westphae/kingfisher/hardware/hat/meta/info.html

# Raspberry Pi HAT

## 40-pin Expansion Board

This project template forms the basis of an expansion board (HAT) for the Raspberry Pi (https://www.raspberrypi.org/) single board computers with a 40-pin GPIO header.
This includes the following models:

- Pi 1 Model A+/B+
- Pi 2 Model B
- Pi 3 Model A+/B/B+
- Pi 4 Model B

Note: for the Pi Zero (W) or smaller designs, see the RaspberryPi-uHAT template.

This project includes a PCB edge set according to the Raspberry Pi HAT Mechanical Specification (https://raw.githubusercontent.com/raspberrypi/hats/master/hat-board-mechanical.pdf) with connectors placed correctly to align the two boards. An alternate edge is included on the User.Drawings layer for the use with an SMT connector. Cutouts have also been defined for the camera and the display cables.

The schematic includes an ID EEPROM chip along with the necessary support components. It does not specify footprints for the ID EEPROM. It is up to the user to choose an appropriate EEPROM chip and footprints.

The official Raspberry Pi HAT Specification (https://github.com/raspberrypi/hats) includes additional information and a design guide.

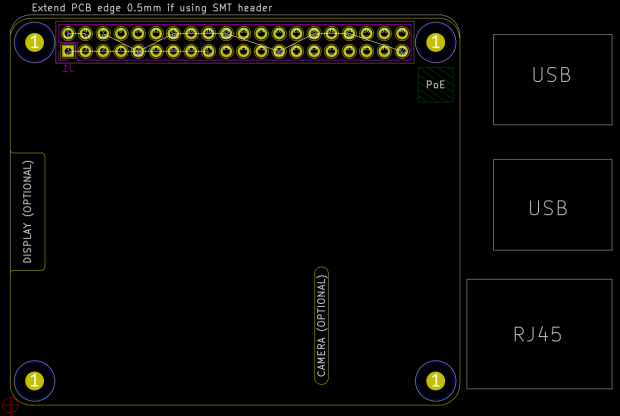
[picture p1: hardware/hat/meta/brd.png]


(c) 2021 Caleb Reister

Adapted from the raspberrypi-gpio-40pin template:
(c) 2016 Ashton Johnson
(c) 2016 Kicad Developers
