westphae/kingfisher/firmware/pod/src/sensors/bq27441.rs

//! SparkFun Battery Babysitter / TI BQ27441-G1A fuel gauge (I²C).
//!
//! Design Capacity and Design Energy are rewritten when ITPOR is set or when
//! the chip still has the G1A factory 1340 mAh. The G1A data memory is RAM-only,
//! so a battery unplug forgets it. Impedance Track initializes Qmax from Design
//! Capacity: Qmax_mAh = QmaxCell0 * DesignCap / 2^14, and Qmax Cell 0 defaults
//! to 16384 Num. Writing learned FCC into offset 0 left FullChargeCapacity
//! stuck at 1340. Default Design Cap is the chem-ID scale and must not change.

use embassy_time::{block_for, Duration, Instant};
use esp_println::println;

use super::bus::Bus as I2cBus;

pub const ADDR: u8 = 0x55;

const CMD_CONTROL: u8 = 0x00;
const CMD_VOLTAGE: u8 = 0x04;
const CMD_FLAGS: u8 = 0x06;
const CMD_REM_CAPACITY: u8 = 0x0c;
const CMD_FULL_CAPACITY: u8 = 0x0e;
const CMD_DESIGN_CAPACITY: u8 = 0x3c;
const CMD_AVG_CURRENT: u8 = 0x10;
const CMD_AVG_POWER: u8 = 0x18;
const CMD_SOC: u8 = 0x1c;

const CTRL_DEVICE_TYPE: u16 = 0x0001;
const CTRL_UNSEAL_KEY: u16 = 0x8000;
const CTRL_SET_CFGUPDATE: u16 = 0x0013;
const CTRL_SOFT_RESET: u16 = 0x0042;

const EXT_CONTROL: u8 = 0x61;
const EXT_DATACLASS: u8 = 0x3e;
const EXT_DATABLOCK: u8 = 0x3f;
const EXT_BLOCKDATA: u8 = 0x40;
const EXT_CHECKSUM: u8 = 0x60;

const ID_STATE: u8 = 82;
const DESIGN_CAPACITY_OFFSET: u8 = 10;
const DESIGN_ENERGY_OFFSET: u8 = 12;
const TERMINATE_VOLTAGE_OFFSET: u8 = 16;

const FLAG_BAT_DET: u16 = 1 << 3;
const CTRL_BAT_INSERT: u16 = 0x000C;

/// G1A ROM default Design Capacity. A matching 0x3C after ITPOR means the
/// host has not reloaded the pack size yet.
const G1A_FACTORY_DESIGN_MAH: u16 = 1340;

/// State subclass stores 16-bit fields MSB-first (TI TRM / SparkFun library).
fn u16_be_bytes(v: u16) -> [u8; 2] {
    [(v >> 8) as u8, (v & 0xff) as u8]
}

/// Design energy (mWh) from mAh at 3.7 V nominal LiPo.
fn design_energy_mwh(mah: u16) -> u16 {
    ((mah as u32) * 37 / 10) as u16
}

const DEVICE_ID: u16 = 0x0421;
const FLAG_ITPOR: u16 = 1 << 5;
const FLAG_CFGUPMODE: u16 = 1 << 4;

const I2C_GAP_US: u64 = 70;
const MIN_READ_INTERVAL_US: u64 = 500_000;

/// One fuel-gauge sample mapped to wire [`Reading::Battery`] units.
#[derive(Debug, Clone, Copy)]
pub struct Sample {
    pub voltage_v: f32,
    pub current_a: f32,
    pub power_w: f32,
    pub capacity_remain_mah: f32,
    pub capacity_full_mah: f32,
    pub soc_pct: f32,
    pub time_remain_s: f32,
    pub design_capacity_mah: u16,
}

pub struct Bq27441 {
    addr: u8,
    last_read_at: Option<Instant>,
}

impl Bq27441 {
    pub fn probe(bus: &mut I2cBus) -> Option<Self> {
        match read_control_word(bus, ADDR, CTRL_DEVICE_TYPE) {
            Ok(id) => {
                println!("pod: i2c 0x{ADDR:02x} device_type=0x{id:04x}");
                if id == DEVICE_ID {
                    return Some(Self {
                        addr: ADDR,
                        last_read_at: None,
                    });
                }
            }
            Err(e) => println!("pod: i2c 0x{ADDR:02x} device_type read: {:?}", e),
        }
        None
    }

    pub fn init(&mut self, bus: &mut I2cBus) -> Result<(), ()> {
        let flags = read_word(bus, self.addr, CMD_FLAGS)?;
        let fcc = read_word(bus, self.addr, CMD_FULL_CAPACITY)?;
        let design_reg = read_design_capacity(bus, self.addr)?;
        let itpor = flags & FLAG_ITPOR != 0;
        // Data memory is RAM: ITPOR means factory defaults (Design ~1340).
        // Restore the baked pack size; Hello can override. Do not write
        // State Qmax Cell 0 — IT seeds Qmax from Design Capacity.
        crate::battery_cfg::note_chip(design_reg);
        let seed = crate::battery_cfg::baked_default();
        // Missed ITPOR still leaves 0x3C at the G1A factory 1340. Treat that
        // as blank when the configured pack is a different size.
        let factory_leftover =
            design_reg == G1A_FACTORY_DESIGN_MAH && seed != G1A_FACTORY_DESIGN_MAH;
        if itpor || design_reg == 0 || factory_leftover {
            println!(
                "pod: bq27441 design_reg={design_reg} (itpor={itpor} fcc={fcc}); restoring design {seed} mAh"
            );
            let _ = crate::battery_cfg::request_design_mah(seed);
        } else {
            println!(
                "pod: bq27441 design capacity {design_reg} mAh (itpor={itpor} fcc={fcc}); trusting gauge RAM"
            );
        }
        self.last_read_at = None;
        println!("pod: bq27441 init ok");
        Ok(())
    }

    /// Reprogram Design Capacity and Design Energy (mAh / mWh) while running.
    /// `qmax_mah` is only for logs — State Qmax Cell 0 is not an mAh seed.
    pub fn program_capacity(&self, bus: &mut I2cBus, design_mah: u16, qmax_mah: u16) -> Result<(), ()> {
        set_capacity_params(bus, self.addr, design_mah, qmax_mah)
    }

    /// Read all headline metrics when the BQ27441 rate limit allows.
    pub fn read_when_due(&mut self, bus: &mut I2cBus) -> Result<Option<Sample>, ()> {
        let now = Instant::now();
        if let Some(prev) = self.last_read_at {
            if now.duration_since(prev).as_micros() < MIN_READ_INTERVAL_US {
                return Ok(None);
            }
        }
        let sample = self.read_sample(bus)?;
        self.last_read_at = Some(now);
        Ok(Some(sample))
    }

    fn read_sample(&self, bus: &mut I2cBus) -> Result<Sample, ()> {
        let voltage_mv = read_word(bus, self.addr, CMD_VOLTAGE)?;
        let capacity_remain = read_word(bus, self.addr, CMD_REM_CAPACITY)?;
        let capacity_full = read_word(bus, self.addr, CMD_FULL_CAPACITY)?;
        let current_ma = read_word_signed(bus, self.addr, CMD_AVG_CURRENT)?;
        let power_mw = read_word_signed(bus, self.addr, CMD_AVG_POWER)?;
        let soc = read_word(bus, self.addr, CMD_SOC)?;
        let design_capacity_mah = read_design_capacity(bus, self.addr)?;

        let voltage_v = voltage_mv as f32 / 1000.0;
        let current_a = current_ma as f32 / 1000.0;
        let power_w = power_mw as f32 / 1000.0;
        let capacity_remain_mah = capacity_remain as f32;
        let capacity_full_mah = capacity_full as f32;
        let soc_pct = soc as f32;

        // mAh / mA -> hours; ×3600 -> seconds (not mAh/A, which is 1000× too large).
        let time_remain_s = if current_ma < -1 {
            (capacity_remain_mah / (current_ma as f32).abs()) * 3600.0
        } else {
            -1.0
        };

        Ok(Sample {
            voltage_v,
            current_a,
            power_w,
            capacity_remain_mah,
            capacity_full_mah,
            soc_pct,
            time_remain_s,
            design_capacity_mah,
        })
    }
}

/// Minimal voltage/current read for the deep-sleep wake check: no init, no
/// rate limiting, no Sample plumbing. None when the gauge doesn't answer.
pub fn quick_check(bus: &mut I2cBus) -> Option<(f32, f32)> {
    let v = read_word(bus, ADDR, CMD_VOLTAGE).ok()?;
    let i = read_word_signed(bus, ADDR, CMD_AVG_CURRENT).ok()?;
    Some((v as f32 / 1000.0, i as f32 / 1000.0))
}

fn i2c_gap() {
    block_for(Duration::from_micros(I2C_GAP_US));
}

fn read_word(bus: &mut I2cBus, addr: u8, reg: u8) -> Result<u16, ()> {
    let mut buf = [0u8; 2];
    bus.write_read(addr, &[reg], &mut buf).map_err(|_| ())?;
    i2c_gap();
    Ok(u16::from_le_bytes(buf))
}

fn read_word_signed(bus: &mut I2cBus, addr: u8, reg: u8) -> Result<i16, ()> {
    Ok(read_word(bus, addr, reg)? as i16)
}

fn write_byte(bus: &mut I2cBus, addr: u8, reg: u8, val: u8) -> Result<(), ()> {
    bus.write(addr, &[reg, val]).map_err(|_| ())?;
    i2c_gap();
    Ok(())
}

fn read_byte(bus: &mut I2cBus, addr: u8, reg: u8) -> Result<u8, ()> {
    let mut buf = [0u8];
    bus.write_read(addr, &[reg], &mut buf).map_err(|_| ())?;
    i2c_gap();
    Ok(buf[0])
}

/// Data-memory Design Capacity (mAh), not learned FullChargeCapacity (0x0E).
fn read_design_capacity(bus: &mut I2cBus, addr: u8) -> Result<u16, ()> {
    read_word(bus, addr, CMD_DESIGN_CAPACITY)
}

fn read_control_word(bus: &mut I2cBus, addr: u8, function: u16) -> Result<u16, ()> {
    let cmd = function.to_le_bytes();
    bus.write(addr, &[CMD_CONTROL, cmd[0], cmd[1]])
        .map_err(|_| ())?;
    i2c_gap();
    read_word(bus, addr, CMD_CONTROL)
}

fn execute_control(bus: &mut I2cBus, addr: u8, function: u16) -> Result<(), ()> {
    let cmd = function.to_le_bytes();
    bus.write(addr, &[CMD_CONTROL, cmd[0], cmd[1]])
        .map_err(|_| ())?;
    i2c_gap();
    Ok(())
}

fn enter_config(bus: &mut I2cBus, addr: u8) -> Result<(), ()> {
    // Unseal twice (SparkFun/TI); required when the gauge is in sealed mode.
    execute_control(bus, addr, CTRL_UNSEAL_KEY)?;
    execute_control(bus, addr, CTRL_UNSEAL_KEY)?;
    execute_control(bus, addr, CTRL_SET_CFGUPDATE)?;
    for _ in 0..2000 {
        let flags = read_word(bus, addr, CMD_FLAGS)?;
        if flags & FLAG_CFGUPMODE != 0 {
            return Ok(());
        }
        block_for(Duration::from_millis(1));
    }
    Err(())
}

fn exit_config_resim(bus: &mut I2cBus, addr: u8) -> Result<(), ()> {
    execute_control(bus, addr, CTRL_SOFT_RESET)?;
    for _ in 0..2000 {
        let flags = read_word(bus, addr, CMD_FLAGS)?;
        if flags & FLAG_CFGUPMODE == 0 {
            return Ok(());
        }
        block_for(Duration::from_millis(1));
    }
    Err(())
}

fn read_block_window(bus: &mut I2cBus, addr: u8) -> Result<[u8; 32], ()> {
    let mut block = [0u8; 32];
    for (i, b) in block.iter_mut().enumerate() {
        *b = read_byte(bus, addr, EXT_BLOCKDATA + i as u8)?;
    }
    Ok(block)
}

fn select_data_block(bus: &mut I2cBus, addr: u8, class_id: u8, offset: u8) -> Result<(), ()> {
    write_byte(bus, addr, EXT_CONTROL, 0x00)?;
    write_byte(bus, addr, EXT_DATACLASS, class_id)?;
    write_byte(bus, addr, EXT_DATABLOCK, offset / 32)?;
    // TI: BlockDataClass must settle before the 32-byte window is valid.
    block_for(Duration::from_millis(5));
    Ok(())
}

fn set_capacity_params(bus: &mut I2cBus, addr: u8, design_mah: u16, qmax_mah: u16) -> Result<(), ()> {
    if enter_config(bus, addr).is_err() {
        log_program_fail(design_mah, qmax_mah, ProgramFail::EnterConfig, 0);
        return Err(());
    }
    if write_design_params(bus, addr, design_mah).is_err() {
        log_program_fail(design_mah, qmax_mah, ProgramFail::WriteBlock, 0);
        let _ = exit_config_resim(bus, addr);
        return Err(());
    }
    if exit_config_resim(bus, addr).is_err() {
        log_program_fail(design_mah, qmax_mah, ProgramFail::ExitConfig, 0);
        return Err(());
    }
    maybe_bat_insert(bus, addr);
    block_for(Duration::from_millis(500));
    for attempt in 0..40 {
        match read_design_capacity(bus, addr) {
            Ok(reg) if reg == design_mah => {
                let fcc = read_word(bus, addr, CMD_FULL_CAPACITY).unwrap_or(0);
                println!(
                    "pod: bq27441 design {design_mah} mAh verified (fcc={fcc} mAh; qmax seed {qmax_mah} not written to State.0)"
                );
                return Ok(());
            }
            Ok(reg) => {
                if attempt == 39 {
                    log_program_fail(design_mah, qmax_mah, ProgramFail::Verify, reg);
                }
            }
            Err(()) => {
                if attempt == 39 {
                    log_program_fail(design_mah, qmax_mah, ProgramFail::Verify, 0);
                }
            }
        }
        block_for(Duration::from_millis(50));
    }
    Err(())
}

fn patch_u16_be(block: &mut [u8; 32], offset: u8, v: u16) {
    let b = u16_be_bytes(v);
    let i = offset as usize;
    block[i] = b[0];
    block[i + 1] = b[1];
}

fn u16_be_at(block: &[u8; 32], offset: u8) -> u16 {
    let i = offset as usize;
    u16::from_be_bytes([block[i], block[i + 1]])
}

fn block_checksum(block: &[u8; 32]) -> u8 {
    let mut sum: u8 = 0;
    for b in block {
        sum = sum.wrapping_add(*b);
    }
    255_u8.wrapping_sub(sum)
}

/// TI example / SparkFun setCapacity: patch Design Capacity (offset 10) and
/// Design Energy (offset 12). Leave Qmax Cell 0 (16384 Num) and Default
/// Design Cap (chem-ID scale) alone.
fn write_design_params(bus: &mut I2cBus, addr: u8, design_mah: u16) -> Result<(), ()> {
    select_data_block(bus, addr, ID_STATE, 0)?;
    let mut block = read_block_window(bus, addr)?;
    let old_design = u16_be_at(&block, DESIGN_CAPACITY_OFFSET);
    let term_v = u16_be_at(&block, TERMINATE_VOLTAGE_OFFSET);
    if !(100..=8000).contains(&old_design) || !(2500..=3700).contains(&term_v) {
        println!(
            "pod: bq27441 state block implausible design={old_design} term_v={term_v}; skip write"
        );
        return Err(());
    }
    let energy = design_energy_mwh(design_mah);
    patch_u16_be(&mut block, DESIGN_CAPACITY_OFFSET, design_mah);
    patch_u16_be(&mut block, DESIGN_ENERGY_OFFSET, energy);

    for i in DESIGN_CAPACITY_OFFSET..=(DESIGN_ENERGY_OFFSET + 1) {
        write_byte(bus, addr, EXT_BLOCKDATA + i, block[i as usize])?;
    }
    block_for(Duration::from_millis(1));
    // SparkFun: checksum from a fresh 32-byte read after the data bytes land.
    let written = read_block_window(bus, addr)?;
    if u16_be_at(&written, DESIGN_CAPACITY_OFFSET) != design_mah {
        println!("pod: bq27441 design patch did not stick in State block");
        return Err(());
    }
    write_byte(bus, addr, EXT_CHECKSUM, block_checksum(&written))?;
    block_for(Duration::from_millis(10));
    Ok(())
}

fn maybe_bat_insert(bus: &mut I2cBus, addr: u8) {
    let Ok(flags) = read_word(bus, addr, CMD_FLAGS) else {
        return;
    };
    if flags & FLAG_BAT_DET == 0 {
        let _ = execute_control(bus, addr, CTRL_BAT_INSERT);
    }
}

#[derive(Copy, Clone)]
enum ProgramFail {
    EnterConfig,
    WriteBlock,
    ExitConfig,
    Verify,
}

fn log_program_fail(target_mah: u16, qmax_mah: u16, stage: ProgramFail, design_reg: u16) {
    let stage_s = match stage {
        ProgramFail::EnterConfig => "enter_config",
        ProgramFail::WriteBlock => "write_block",
        ProgramFail::ExitConfig => "exit_config",
        ProgramFail::Verify => "verify_design_reg",
    };
    println!(
        "pod: bq27441 capacity program fail stage={stage_s} design={target_mah} qmax={qmax_mah} design_reg=0x{design_reg:04x} ({design_reg})"
    );
}
