westphae/kingfisher/firmware/pod/build.rs

//! Reads kingfisher config.json at build time and injects pod WiFi/UDP settings
//! into the firmware via cargo:rustc-env (consumed by src/cfg.rs env!).

use std::env;
use std::fs;
use std::path::PathBuf;

use serde::Deserialize;

const DEFAULT_UDP: &str = "192.168.10.1:47808";

#[derive(Debug, Deserialize, Default)]
struct FileConfig {
    #[serde(default)]
    pod: PodSection,
    #[serde(default, rename = "pod_udp_addr")]
    pod_udp_addr: String,
}

#[derive(Debug, Deserialize, Default)]
struct PodSection {
    #[serde(default, rename = "wifi_ssid")]
    wifi_ssid: String,
    #[serde(default, rename = "wifi_password")]
    wifi_password: String,
    #[serde(default, rename = "udp_addr")]
    udp_addr: String,
    #[serde(default = "default_battery_capacity", rename = "battery_capacity_mah")]
    battery_capacity_mah: u16,
    #[serde(default = "default_burst_soc_pct", rename = "burst_soc_pct")]
    burst_soc_pct: u8,
    #[serde(default = "default_burst_window_s", rename = "burst_window_s")]
    burst_window_s: u16,
    #[serde(
        default = "default_burst_voltage_uncal",
        rename = "burst_voltage_v_uncalibrated"
    )]
    burst_voltage_v_uncalibrated: f32,
    #[serde(default = "default_protect_voltage", rename = "protect_voltage_v")]
    protect_voltage_v: f32,
    #[serde(default = "default_protect_soc_pct", rename = "protect_soc_pct")]
    protect_soc_pct: u8,
    #[serde(default = "default_low_debounce_s", rename = "low_debounce_s")]
    low_debounce_s: u16,
    // Default OFF: bench test 2026-07-14 showed PowerSaveMode::Minimum breaks
    // AP→pod unicast delivery on the Pi's brcmfmac AP (pod misses all Cmd/Ping
    // frames; re-Hellos every 30 s; SetRate never applies).
    #[serde(default, rename = "modem_power_save")]
    modem_power_save: bool,
    #[serde(default = "default_flush_interval_s", rename = "flush_interval_s")]
    flush_interval_s: u16,
    #[serde(default = "default_flush_watermark", rename = "flush_high_watermark")]
    flush_high_watermark: u16,
    #[serde(default = "default_buffer_max", rename = "buffer_max_readings")]
    buffer_max_readings: u16,
}

fn default_battery_capacity() -> u16 {
    850
}

fn default_burst_soc_pct() -> u8 {
    30
}
fn default_burst_window_s() -> u16 {
    60
}
fn default_burst_voltage_uncal() -> f32 {
    3.60
}
fn default_protect_voltage() -> f32 {
    3.50
}
fn default_protect_soc_pct() -> u8 {
    5
}
fn default_low_debounce_s() -> u16 {
    45
}
fn default_flush_interval_s() -> u16 {
    3
}
fn default_flush_watermark() -> u16 {
    24
}
fn default_buffer_max() -> u16 {
    128
}

fn main() {
    let config_path = resolve_config_path();
    let raw = fs::read_to_string(&config_path).unwrap_or_else(|e| {
        panic!(
            "pod firmware build: read config {}: {e}\n\
             Set KINGFISHER_CONFIG to your kingfisher config.json path.",
            config_path.display()
        );
    });

    let cfg: FileConfig = serde_json::from_str(&raw).unwrap_or_else(|e| {
        panic!(
            "pod firmware build: parse config {}: {e}",
            config_path.display()
        );
    });

    let mut udp_addr = cfg.pod.udp_addr;
    if udp_addr.is_empty() {
        udp_addr = cfg.pod_udp_addr;
    }
    if udp_addr.is_empty() {
        udp_addr = DEFAULT_UDP.to_string();
    }

    let ssid = cfg.pod.wifi_ssid;
    if ssid.is_empty() {
        panic!(
            "pod firmware build: config {} missing pod.wifi_ssid\n\
             Add a \"pod\" section with wifi_ssid, wifi_password, and udp_addr.",
            config_path.display()
        );
    }

    validate_no_newlines("pod.wifi_ssid", &ssid);
    validate_no_newlines("pod.wifi_password", &cfg.pod.wifi_password);
    validate_udp_addr(&udp_addr);

    println!("cargo:rerun-if-changed={}", config_path.display());
    println!("cargo:rerun-if-env-changed=KINGFISHER_CONFIG");
    println!("cargo:rustc-env=SSID={ssid}");
    println!("cargo:rustc-env=PASSWORD={}", cfg.pod.wifi_password);
    println!("cargo:rustc-env=PI_ADDR={udp_addr}");
    println!(
        "cargo:rustc-env=BATTERY_CAPACITY_MAH={}",
        cfg.pod.battery_capacity_mah
    );
    println!("cargo:rustc-env=BURST_SOC_PCT={}", cfg.pod.burst_soc_pct);
    println!("cargo:rustc-env=BURST_WINDOW_S={}", cfg.pod.burst_window_s);
    println!(
        "cargo:rustc-env=BURST_VOLTAGE_UNCAL={:.3}",
        cfg.pod.burst_voltage_v_uncalibrated
    );
    println!(
        "cargo:rustc-env=PROTECT_VOLTAGE={:.3}",
        cfg.pod.protect_voltage_v
    );
    println!(
        "cargo:rustc-env=PROTECT_SOC_PCT={}",
        cfg.pod.protect_soc_pct
    );
    println!("cargo:rustc-env=LOW_DEBOUNCE_S={}", cfg.pod.low_debounce_s);
    println!(
        "cargo:rustc-env=MODEM_POWER_SAVE={}",
        if cfg.pod.modem_power_save { "1" } else { "0" }
    );
    println!(
        "cargo:rustc-env=FLUSH_INTERVAL_S={}",
        cfg.pod.flush_interval_s
    );
    println!(
        "cargo:rustc-env=FLUSH_HIGH_WATERMARK={}",
        cfg.pod.flush_high_watermark
    );
    println!(
        "cargo:rustc-env=BUFFER_MAX_READINGS={}",
        cfg.pod.buffer_max_readings
    );
}

fn resolve_config_path() -> PathBuf {
    if let Ok(p) = env::var("KINGFISHER_CONFIG") {
        return PathBuf::from(p);
    }
    let home = env::var("HOME").unwrap_or_else(|_| {
        panic!("pod firmware build: HOME not set; export KINGFISHER_CONFIG=/path/to/config.json");
    });
    PathBuf::from(home)
        .join(".config")
        .join("kingfisher")
        .join("config.json")
}

fn validate_no_newlines(field: &str, value: &str) {
    if value.contains('\n') || value.contains('\r') {
        panic!("pod firmware build: {field} must not contain newlines");
    }
}

fn validate_udp_addr(addr: &str) {
    let Some((host, port)) = addr.rsplit_once(':') else {
        panic!("pod firmware build: pod.udp_addr must be host:port, got {addr:?}");
    };
    if host.is_empty() || port.is_empty() {
        panic!("pod firmware build: pod.udp_addr must be host:port, got {addr:?}");
    }
    if !port.bytes().all(|b| b.is_ascii_digit()) {
        panic!("pod firmware build: invalid port in pod.udp_addr {addr:?}");
    }
    let parts: Vec<_> = host.split('.').collect();
    if parts.len() != 4 {
        panic!("pod firmware build: pod.udp_addr host must be IPv4, got {addr:?}");
    }
}
